raspberrypilearning/build-your-own-weather-station/en/images/2017-12-06-140025_1680x1050_scrot.png

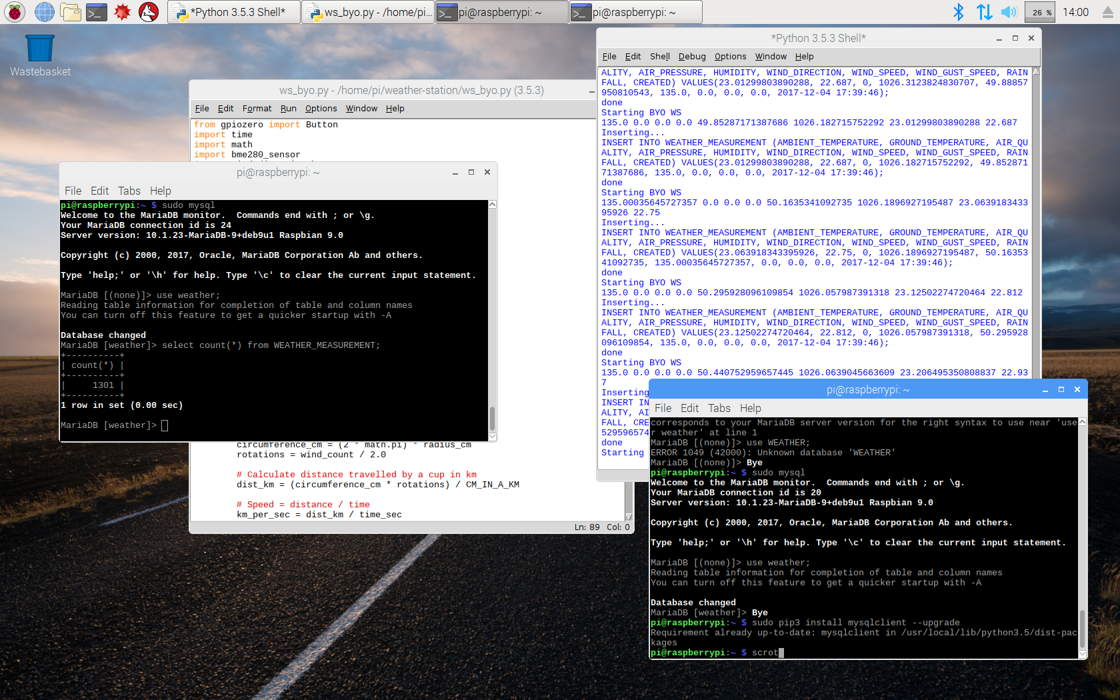
en/images/2017-12-06-140025_1680x1050_scrot.png
