raspberrypilearning/build-your-own-weather-station/en/images/BYO_breadboard2.JPG

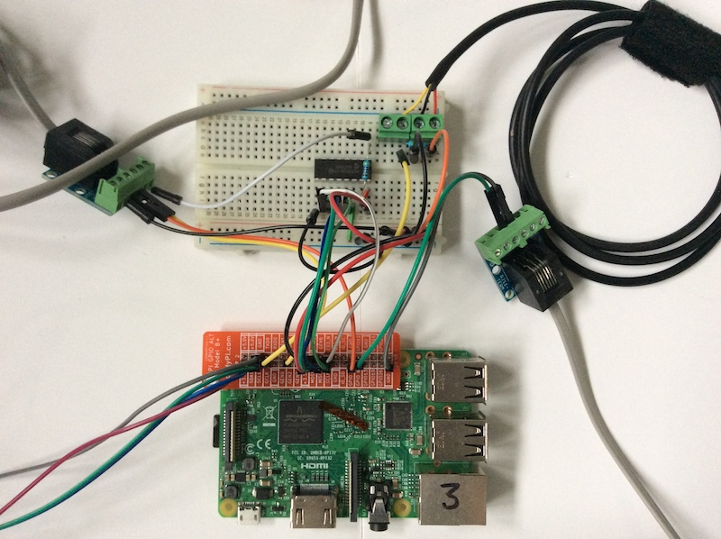
en/images/BYO_breadboard2.JPG
