raspberrypilearning/build-your-own-weather-station/en/images/dht22_bb.png

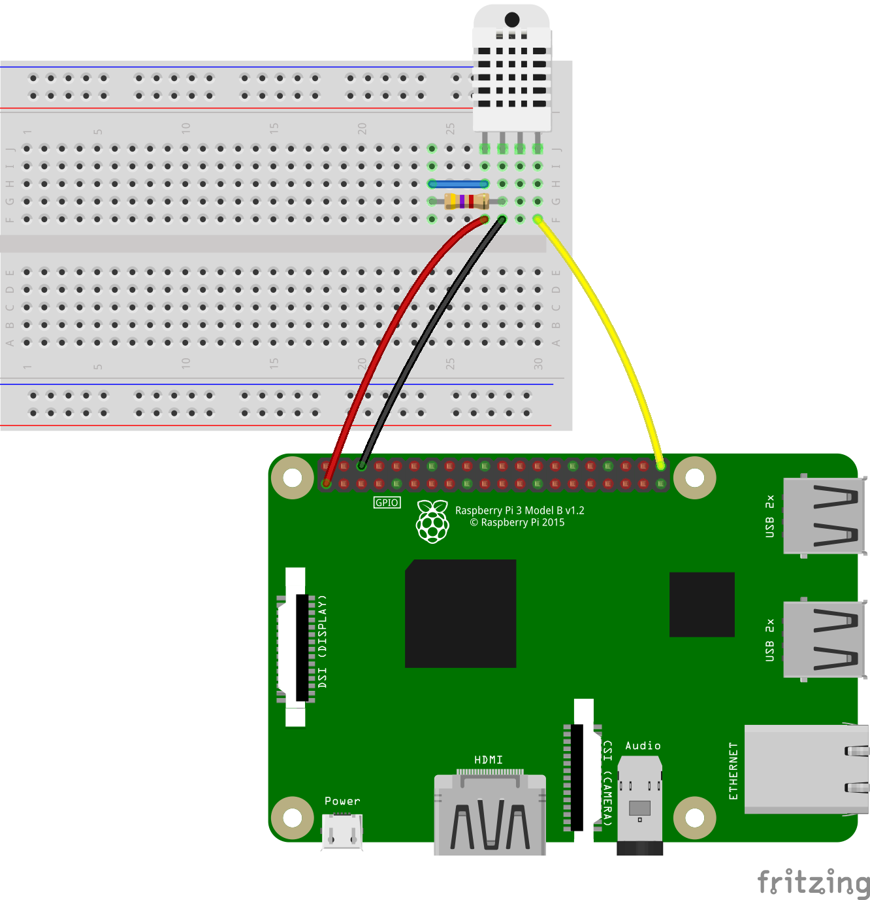
en/images/dht22_bb.png
