raspberrypilearning/build-your-own-weather-station/en/images/dht22_code_run.png

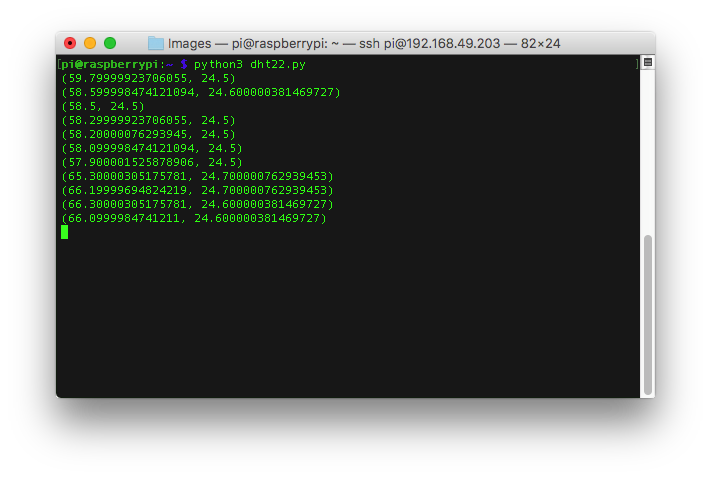
en/images/dht22_code_run.png
