raspberrypilearning/build-your-own-weather-station/en/images/final_circuit_bb.png

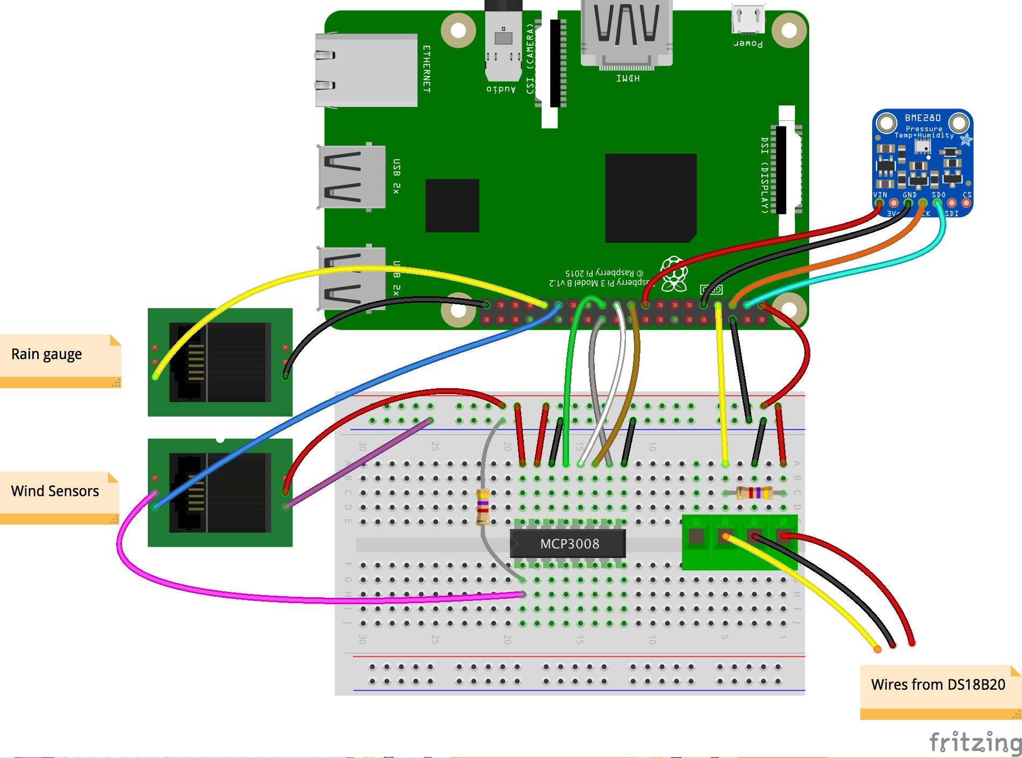
en/images/final_circuit_bb.png
