raspberrypilearning/build-your-own-weather-station/en/images/htu21d_bb.png

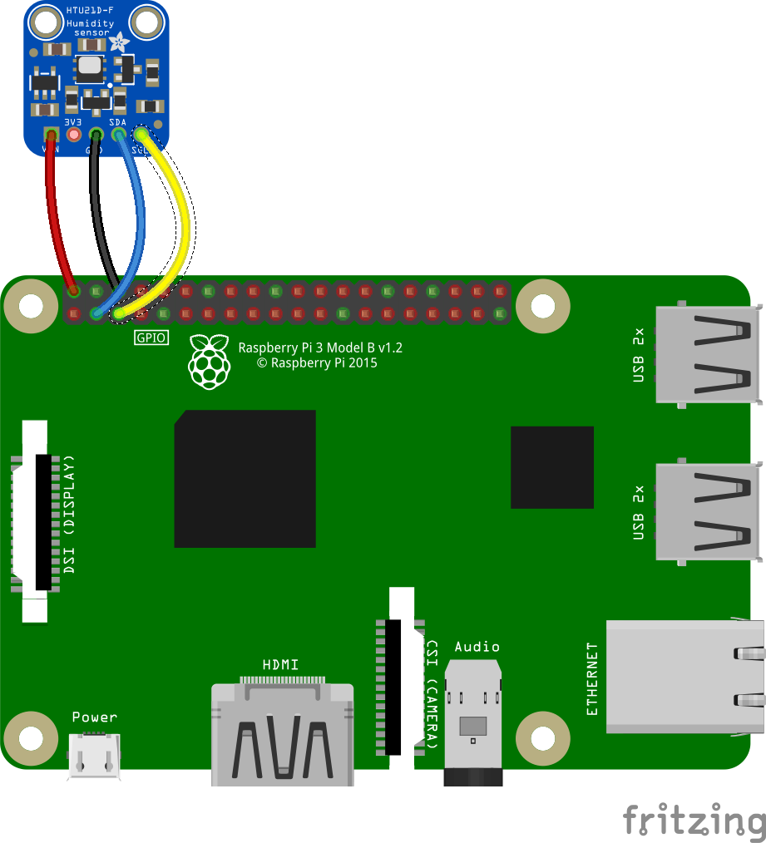
en/images/htu21d_bb.png
