raspberrypilearning/build-your-own-weather-station/en/images/humtemp_code_run.png

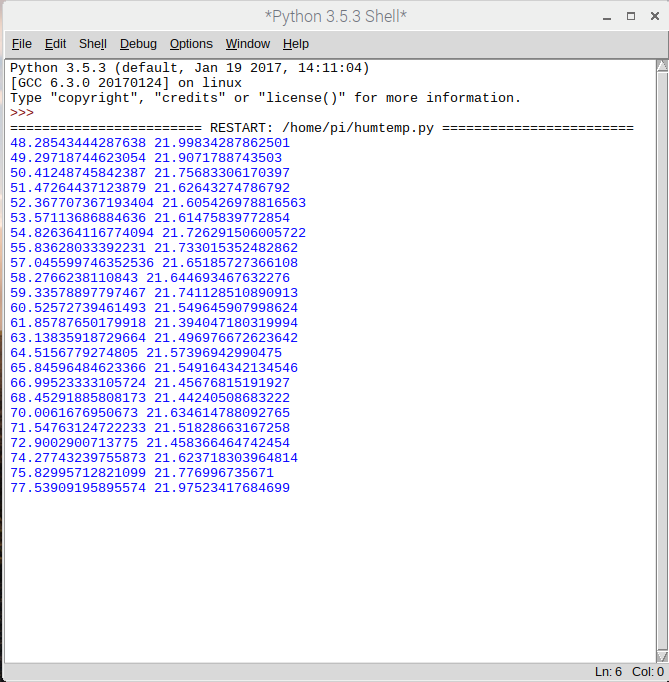
en/images/humtemp_code_run.png
