raspberrypilearning/build-your-own-weather-station/en/images/IMG_3933.JPG

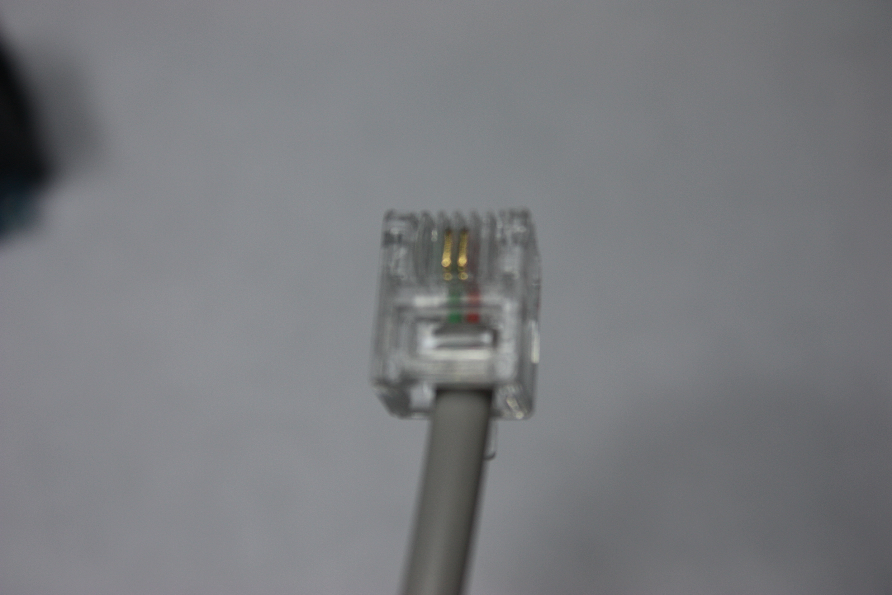
en/images/IMG_3933.JPG
