raspberrypilearning/build-your-own-weather-station/en/images/MCP3008_bb.png

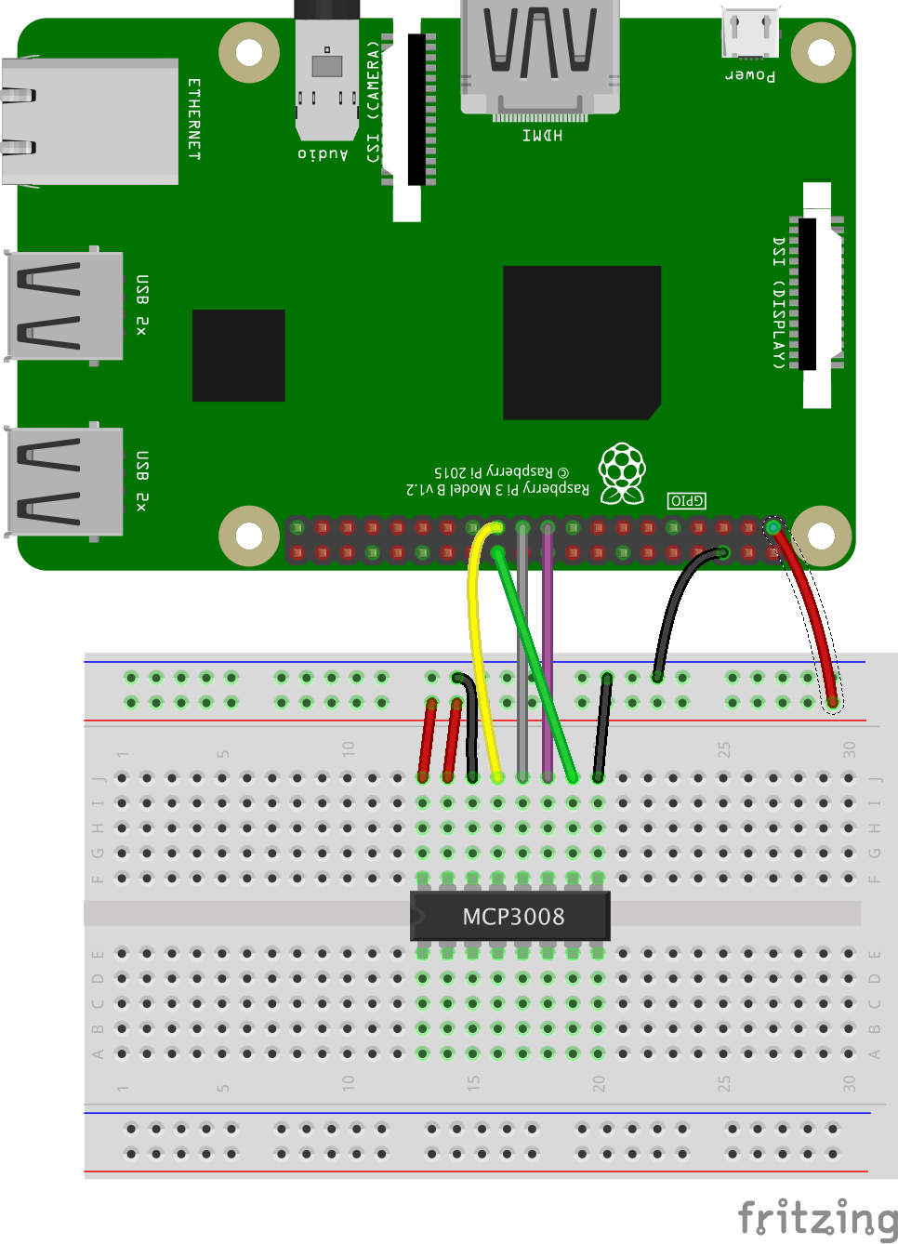
en/images/MCP3008_bb.png
