raspberrypilearning/build-your-own-weather-station/en/images/MCP3008_vane_bb.png

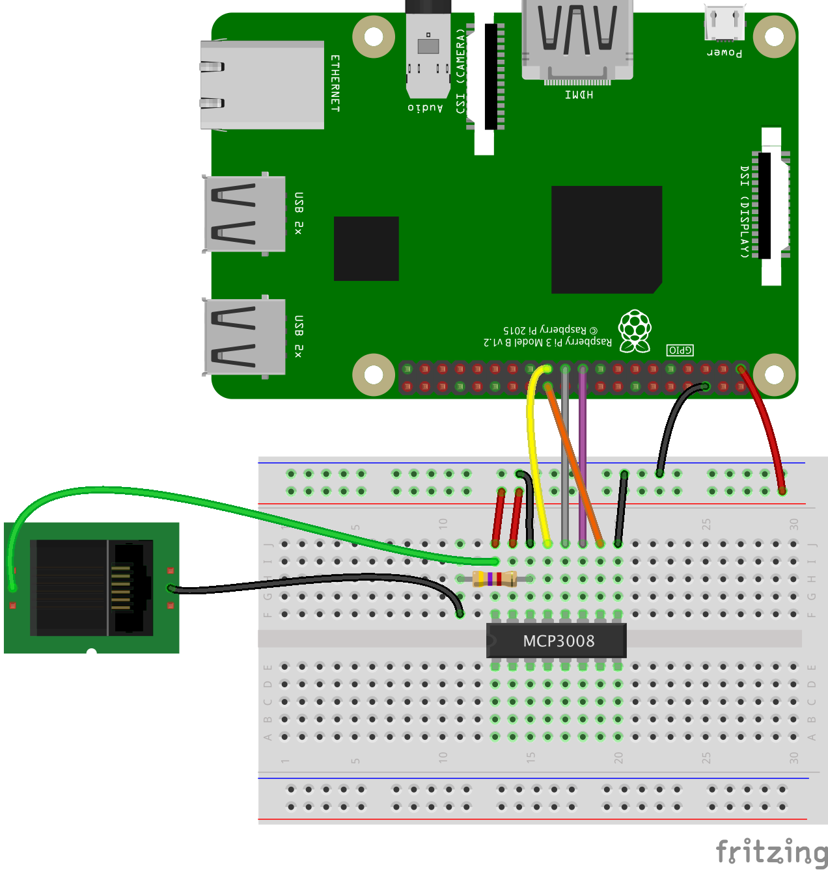
en/images/MCP3008_vane_bb.png
