raspberrypilearning/build-your-own-weather-station/en/images/screw_terminals.png

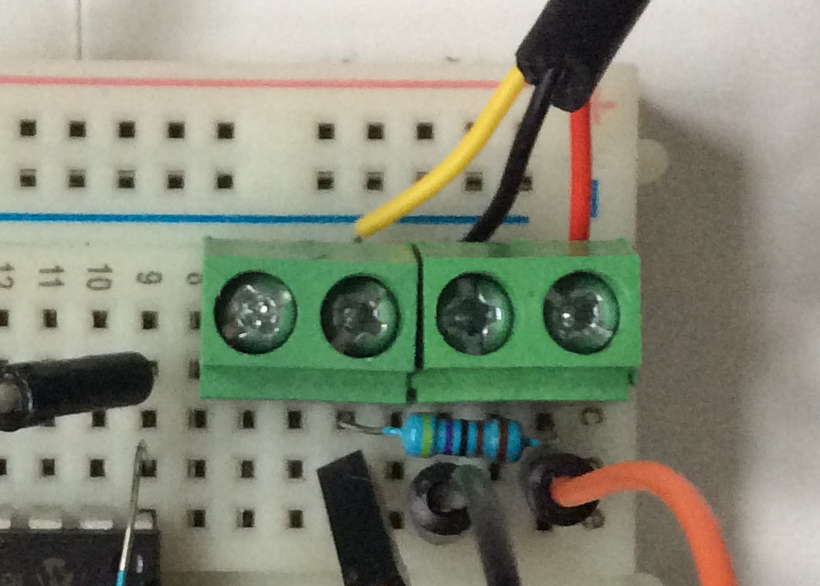
en/images/screw_terminals.png
